jonelay/chibi-ecen-bms/analysis/diagrams/conops_visual.jpg

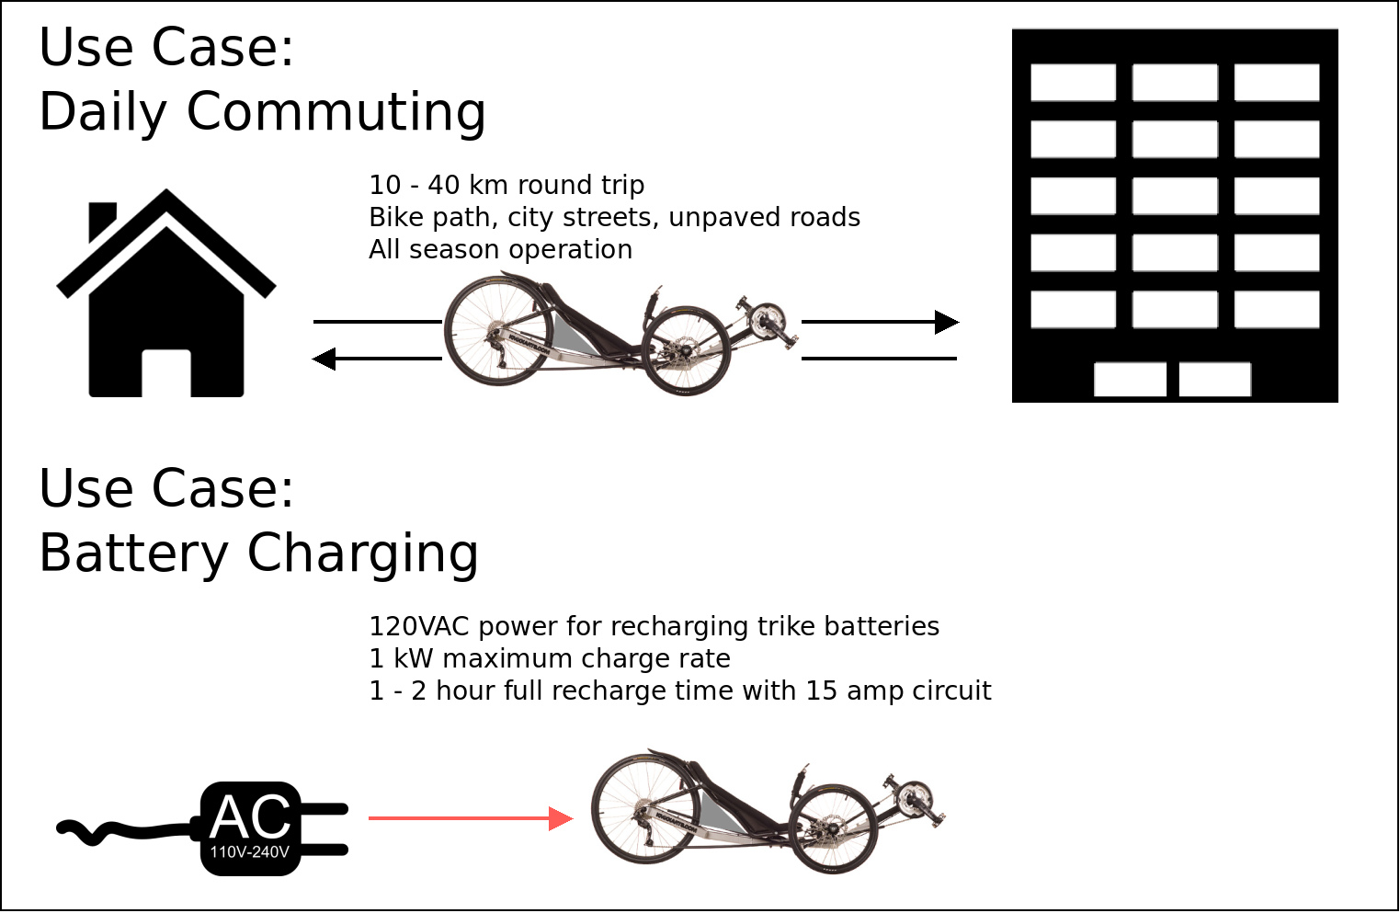
analysis/diagrams/conops_visual.jpg
