jonelay/chibi-ecen-bms/design-source/mechanical/solidworks/18650.SLDPRT

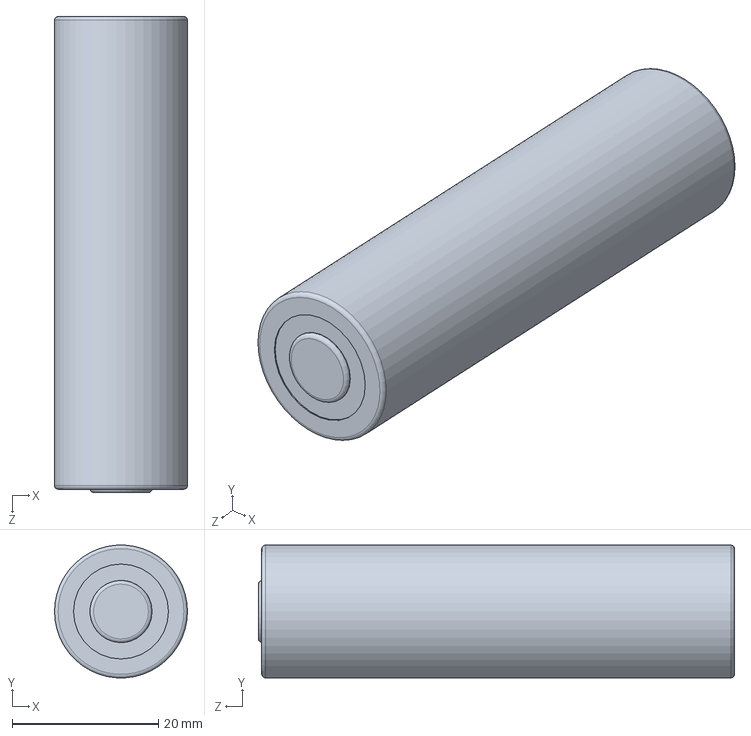
[picture p40: CAD file, 2026-01-08]
design-source/mechanical/solidworks/18650.SLDPRT
18.2 x 18.2 x 65.2 mm
